perrypetiet/EasyDSP/device_firmware/main/dsp_defines/sigma_dsp_module_data.h

#ifndef SIGMA_DSP_MODULE_DATA_H_
#define SIGMA_DSP_MODULE_DATA_H_

#define ADA_COEFFICIENT_AMOUNT                   5

/* Module input1_eq - Medium Size Eq*/
#define MOD_INPUT1_EQ_COUNT                      25
#define MOD_INPUT1_EQ_ALG0_STAGE0_B0_ADDR        0
#define MOD_INPUT1_EQ_ALG0_STAGE0_B0_FIXPT       0x00800000
#define MOD_INPUT1_EQ_ALG0_STAGE0_B1_ADDR        1
#define MOD_INPUT1_EQ_ALG0_STAGE0_B1_FIXPT       0x00000000
#define MOD_INPUT1_EQ_ALG0_STAGE0_B2_ADDR        2
#define MOD_INPUT1_EQ_ALG0_STAGE0_B2_FIXPT       0x00000000
#define MOD_INPUT1_EQ_ALG0_STAGE0_A0_ADDR        3
#define MOD_INPUT1_EQ_ALG0_STAGE0_A0_FIXPT       0x00000000
#define MOD_INPUT1_EQ_ALG0_STAGE0_A1_ADDR        4
#define MOD_INPUT1_EQ_ALG0_STAGE0_A1_FIXPT       0x00000000
#define MOD_INPUT1_EQ_ALG0_STAGE1_B0_ADDR        5
#define MOD_INPUT1_EQ_ALG0_STAGE1_B0_FIXPT       0x00800000
#define MOD_INPUT1_EQ_ALG0_STAGE1_B1_ADDR        6
#define MOD_INPUT1_EQ_ALG0_STAGE1_B1_FIXPT       0x00000000
#define MOD_INPUT1_EQ_ALG0_STAGE1_B2_ADDR        7
#define MOD_INPUT1_EQ_ALG0_STAGE1_B2_FIXPT       0x00000000
#define MOD_INPUT1_EQ_ALG0_STAGE1_A0_ADDR        8
#define MOD_INPUT1_EQ_ALG0_STAGE1_A0_FIXPT       0x00000000
#define MOD_INPUT1_EQ_ALG0_STAGE1_A1_ADDR        9
#define MOD_INPUT1_EQ_ALG0_STAGE1_A1_FIXPT       0x00000000
#define MOD_INPUT1_EQ_ALG0_STAGE2_B0_ADDR        10
#define MOD_INPUT1_EQ_ALG0_STAGE2_B0_FIXPT       0x00800000
#define MOD_INPUT1_EQ_ALG0_STAGE2_B1_ADDR        11
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
#define MOD_OUTPUT4_EQ_ALG0_STAGE3_B2_ADDR       147
#define MOD_OUTPUT4_EQ_ALG0_STAGE3_B2_FIXPT      0x00000000
#define MOD_OUTPUT4_EQ_ALG0_STAGE3_A0_ADDR       148
#define MOD_OUTPUT4_EQ_ALG0_STAGE3_A0_FIXPT      0x00000000
#define MOD_OUTPUT4_EQ_ALG0_STAGE3_A1_ADDR       149
#define MOD_OUTPUT4_EQ_ALG0_STAGE3_A1_FIXPT      0x00000000
#define MOD_OUTPUT4_EQ_ALG0_STAGE4_B0_ADDR       150
#define MOD_OUTPUT4_EQ_ALG0_STAGE4_B0_FIXPT      0x00800000
#define MOD_OUTPUT4_EQ_ALG0_STAGE4_B1_ADDR       151
#define MOD_OUTPUT4_EQ_ALG0_STAGE4_B1_FIXPT      0x00000000
#define MOD_OUTPUT4_EQ_ALG0_STAGE4_B2_ADDR       152
#define MOD_OUTPUT4_EQ_ALG0_STAGE4_B2_FIXPT      0x00000000
#define MOD_OUTPUT4_EQ_ALG0_STAGE4_A0_ADDR       153
#define MOD_OUTPUT4_EQ_ALG0_STAGE4_A0_FIXPT      0x00000000
#define MOD_OUTPUT4_EQ_ALG0_STAGE4_A1_ADDR       154
#define MOD_OUTPUT4_EQ_ALG0_STAGE4_A1_FIXPT      0x00000000
/* Module output1_gain - Single SW slew vol (adjustable)*/
#define MOD_OUTPUT1_GAIN_COUNT             2
#define MOD_OUTPUT1_GAIN_ALG0_TARGET_ADDR        155
#define MOD_OUTPUT1_GAIN_ALG0_TARGET_FIXPT       0x00800000
#define MOD_OUTPUT1_GAIN_ALG0_STEP_ADDR        156
#define MOD_OUTPUT1_GAIN_ALG0_STEP_FIXPT         0x00000800
/* Module output2_gain - Single SW slew vol (adjustable)*/
#define MOD_OUTPUT2_GAIN_COUNT             2
#define MOD_OUTPUT2_GAIN_ALG0_TARGET_ADDR        157
#define MOD_OUTPUT2_GAIN_ALG0_TARGET_FIXPT       0x00800000
#define MOD_OUTPUT2_GAIN_ALG0_STEP_ADDR        158
#define MOD_OUTPUT2_GAIN_ALG0_STEP_FIXPT         0x00000800
/* Module output3_gain - Single SW slew vol (adjustable)*/
#define MOD_OUTPUT3_GAIN_COUNT             2
#define MOD_OUTPUT3_GAIN_ALG0_TARGET_ADDR        159
#define MOD_OUTPUT3_GAIN_ALG0_TARGET_FIXPT       0x00800000
#define MOD_OUTPUT3_GAIN_ALG0_STEP_ADDR        160
#define MOD_OUTPUT3_GAIN_ALG0_STEP_FIXPT         0x00000800
/* Module output4_gain - Single SW slew vol (adjustable)*/
#define MOD_OUTPUT4_GAIN_COUNT             2
#define MOD_OUTPUT4_GAIN_ALG0_TARGET_ADDR        161
#define MOD_OUTPUT4_GAIN_ALG0_TARGET_FIXPT       0x00800000
#define MOD_OUTPUT4_GAIN_ALG0_STEP_ADDR        162
#define MOD_OUTPUT4_GAIN_ALG0_STEP_FIXPT         0x00000800


#endif /* SIGMA_DSP_MODULE_DATA_H_ */
