perrypetiet/EasyDSP/device_firmware/sigma_studio_project/export/easydsp_IC_1.h

/*
 * File:           C:\Users\perry\Documents\GitHub\EasyDSP\device_firmware\sigma_studio_project\export\easydsp_IC_1.h
 *
 * Created:        Thursday, November 9, 2023 1:23:58 PM
 * Description:    easydsp:IC 1 program data.
 *
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
 * This software may only be used to program products purchased from
 * Analog Devices for incorporation by you into audio products that
 * are intended for resale to audio product end users. This software
 * may not be distributed whole or in any part to third parties.
 *
 * Copyright ©2023 Analog Devices, Inc. All rights reserved.
 */
#ifndef __EASYDSP_IC_1_H__
#define __EASYDSP_IC_1_H__

#include "SigmaStudioFW.h"
#include "easydsp_IC_1_REG.h"

#define DEVICE_ARCHITECTURE_IC_1                  "ADAU1701"
#define DEVICE_ADDR_IC_1                          0x68

/* DSP Program Data */
#define PROGRAM_SIZE_IC_1 5120
#define PROGRAM_ADDR_IC_1 1024
ADI_REG_TYPE Program_Data_IC_1[PROGRAM_SIZE_IC_1] = {
0x00, 0x00, 0x00, 0x00, 0x01, 
0x00, 0x10, 0x00, 0xE8, 0x01, 
0x00, 0x00, 0x00, 0x00, 0x01, 
0x01, 0x18, 0x00, 0xE8, 0x01, 
0x00, 0x3A, 0x03, 0x20, 0x01, 
0x00, 0x32, 0x04, 0x22, 0x01, 
0x00, 0x22, 0x03, 0x34, 0x01, 
0x00, 0x1A, 0x04, 0x22, 0x01, 
0x00, 0x12, 0x00, 0x22, 0x01, 
0x00, 0x0A, 0x01, 0x22, 0x01, 
0x00, 0x02, 0x02, 0x22, 0x01, 
0x00, 0x00, 0x00, 0x00, 0x01, 
0x00, 0x28, 0x00, 0xE2, 0x01, 
0x00, 0x40, 0x00, 0xF2, 0x01, 
0x00, 0x6A, 0x08, 0x20, 0x01, 
0x00, 0x62, 0x09, 0x22, 0x01, 
0x00, 0x52, 0x08, 0x34, 0x01, 
0x00, 0x4A, 0x09, 0x22, 0x01, 
0x00, 0x2A, 0x05, 0x22, 0x01, 
0x00, 0x22, 0x06, 0x22, 0x01, 
0x00, 0x1A, 0x07, 0x22, 0x01, 
0x00, 0x00, 0x00, 0x00, 0x01, 
0x00, 0x58, 0x00, 0xE2, 0x01, 
0x00, 0x70, 0x00, 0xF2, 0x01, 
0x00, 0x9A, 0x0D, 0x20, 0x01, 
0x00, 0x92, 0x0E, 0x22, 0x01, 
0x00, 0x82, 0x0D, 0x34, 0x01, 
0x00, 0x7A, 0x0E, 0x22, 0x01, 
0x00, 0x5A, 0x0A, 0x22, 0x01, 
0x00, 0x52, 0x0B, 0x22, 0x01, 
0x00, 0x4A, 0x0C, 0x22, 0x01, 
0x00, 0x00, 0x00, 0x00, 0x01, 
0x00, 0x88, 0x00, 0xE2, 0x01, 
0x00, 0xA0, 0x00, 0xF2, 0x01, 
0x00, 0xCA, 0x12, 0x20, 0x01, 
0x00, 0xC2, 0x13, 0x22, 0x01, 
0x00, 0xB2, 0x12, 0x34, 0x01, 
0x00, 0xAA, 0x13, 0x22, 0x01, 
0x00, 0x8A, 0x0F, 0x22, 0x01, 
0x00, 0x82, 0x10, 0x22, 0x01, 
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
};

/* DSP Parameter (Coefficient) Data */
#define PARAM_SIZE_IC_1 4096
#define PARAM_ADDR_IC_1 0
ADI_REG_TYPE Param_Data_IC_1[PARAM_SIZE_IC_1] = {
0x00, 0x80, 0x00, 0x00, 
0x00, 0x00, 0x00, 0x00, 
0x00, 0x00, 0x00, 0x00, 
0x00, 0x00, 0x00, 0x00, 
0x00, 0x00, 0x00, 0x00, 
0x00, 0x80, 0x00, 0x00, 
0x00, 0x00, 0x00, 0x00, 
0x00, 0x00, 0x00, 0x00, 
0x00, 0x00, 0x00, 0x00, 
0x00, 0x00, 0x00, 0x00, 
0x00, 0x80, 0x00, 0x00, 
0x00, 0x00, 0x00, 0x00, 
0x00, 0x00, 0x00, 0x00, 
0x00, 0x00, 0x00, 0x00, 
0x00, 0x00, 0x00, 0x00, 
0x00, 0x80, 0x00, 0x00, 
0x00, 0x00, 0x00, 0x00, 
0x00, 0x00, 0x00, 0x00, 
0x00, 0x00, 0x00, 0x00, 
0x00, 0x00, 0x00, 0x00, 
0x00, 0x80, 0x00, 0x00, 
0x00, 0x00, 0x00, 0x00, 
0x00, 0x00, 0x00, 0x00, 
0x00, 0x00, 0x00, 0x00, 
0x00, 0x00, 0x00, 0x00, 
0x00, 0x80, 0x00, 0x00, 
0x00, 0x00, 0x00, 0x00, 
0x00, 0x00, 0x00, 0x00, 
0x00, 0x00, 0x00, 0x00, 
0x00, 0x00, 0x00, 0x00, 
0x00, 0x80, 0x00, 0x00, 
0x00, 0x00, 0x00, 0x00, 
0x00, 0x00, 0x00, 0x00, 
0x00, 0x00, 0x00, 0x00, 
0x00, 0x00, 0x00, 0x00, 
0x00, 0x80, 0x00, 0x00, 
0x00, 0x00, 0x00, 0x00, 
0x00, 0x00, 0x00, 0x00, 
0x00, 0x00, 0x00, 0x00, 
0x00, 0x00, 0x00, 0x00, 
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
};


/* Register Default - IC 1.CoreRegister */
ADI_REG_TYPE R0_COREREGISTER_IC_1_Default[REG_COREREGISTER_IC_1_BYTE] = {
0x00, 0x18
};

/* Register Default - IC 1.HWConFiguration */
#define R3_HWCONFIGURATION_IC_1_SIZE 24
ADI_REG_TYPE R3_HWCONFIGURATION_IC_1_Default[R3_HWCONFIGURATION_IC_1_SIZE] = {
0x00, 0x18, 0x08, 0x00, 0x00, 0x00, 0x00, 0x00, 0x00, 0x00, 0x00, 0x00, 0x00, 0x00, 0x00, 0x00, 0x80, 0x00, 0x00, 0x00, 0x00, 0x00, 0x00, 0x01
};

/* Register Default - IC 1.CoreRegister */
ADI_REG_TYPE R4_COREREGISTER_IC_1_Default[REG_COREREGISTER_IC_1_BYTE] = {
0x00, 0x1C
};


/*
 * Default Download
 */
#define DEFAULT_DOWNLOAD_SIZE_IC_1 5

void default_download_IC_1() {
	SIGMA_WRITE_REGISTER_BLOCK( DEVICE_ADDR_IC_1, REG_COREREGISTER_IC_1_ADDR, REG_COREREGISTER_IC_1_BYTE, R0_COREREGISTER_IC_1_Default );
	SIGMA_WRITE_REGISTER_BLOCK( DEVICE_ADDR_IC_1, PROGRAM_ADDR_IC_1, PROGRAM_SIZE_IC_1, Program_Data_IC_1 );
	SIGMA_WRITE_REGISTER_BLOCK( DEVICE_ADDR_IC_1, PARAM_ADDR_IC_1, PARAM_SIZE_IC_1, Param_Data_IC_1 );
	SIGMA_WRITE_REGISTER_BLOCK( DEVICE_ADDR_IC_1, REG_COREREGISTER_IC_1_ADDR , R3_HWCONFIGURATION_IC_1_SIZE, R3_HWCONFIGURATION_IC_1_Default );
	SIGMA_WRITE_REGISTER_BLOCK( DEVICE_ADDR_IC_1, REG_COREREGISTER_IC_1_ADDR, REG_COREREGISTER_IC_1_BYTE, R4_COREREGISTER_IC_1_Default );
}

#endif
