perrypetiet/EasyDSP/device_firmware/main/crc16.c

/*
 * Library: libcrc
 * File:    src/crc16.c
 * Author:  Lammert Bies
 *
 * This file is licensed under the MIT License as stated below
 *
 * Copyright (c) 1999-2016 Lammert Bies
 *
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
 * Description
 * -----------
 * The source file src/crc16.c contains routines which calculate the common
 * CRC16 cyclic redundancy check values for an incomming byte string.
 */

#include <stdbool.h>
#include <stdlib.h>
#include "crc16.h"

static void             init_crc16_tab( void );

static bool             crc_tab16_init          = false;
static uint16_t         crc_tab16[256];

/*
 * uint16_t crc_16( const unsigned char *input_str, size_t num_bytes );
 *
 * The function crc_16() calculates the 16 bits CRC16 in one pass for a byte
 * string of which the beginning has been passed to the function. The number of
 * bytes to check is also a parameter. The number of the bytes in the string is
 * limited by the constant SIZE_MAX.
 */

uint16_t crc_16( const unsigned char *input_str, size_t num_bytes ) {

	uint16_t crc;
	const unsigned char *ptr;
	size_t a;

	if ( ! crc_tab16_init ) init_crc16_tab();

	crc = CRC_START_16;
	ptr = input_str;

	if ( ptr != NULL ) for (a=0; a<num_bytes; a++) {

		crc = (crc >> 8) ^ crc_tab16[ (crc ^ (uint16_t) *ptr++) & 0x00FF ];
	}

	return crc;

}  /* crc_16 */

/*
 * uint16_t crc_modbus( const unsigned char *input_str, size_t num_bytes );
 *
 * The function crc_modbus() calculates the 16 bits Modbus CRC in one pass for
 * a byte string of which the beginning has been passed to the function. The
 * number of bytes to check is also a parameter.
 */

uint16_t crc_modbus( const unsigned char *input_str, size_t num_bytes ) {

	uint16_t crc;
	const unsigned char *ptr;
	size_t a;

	if ( ! crc_tab16_init ) init_crc16_tab();

	crc = CRC_START_MODBUS;
	ptr = input_str;

	if ( ptr != NULL ) for (a=0; a<num_bytes; a++) {

		crc = (crc >> 8) ^ crc_tab16[ (crc ^ (uint16_t) *ptr++) & 0x00FF ];
	}

	return crc;

}  /* crc_modbus */

/*
 * uint16_t update_crc_16( uint16_t crc, unsigned char c );
 *
 * The function update_crc_16() calculates a new CRC-16 value based on the
 * previous value of the CRC and the next byte of data to be checked.
 */

uint16_t update_crc_16( uint16_t crc, unsigned char c ) {

	if ( ! crc_tab16_init ) init_crc16_tab();

	return (crc >> 8) ^ crc_tab16[ (crc ^ (uint16_t) c) & 0x00FF ];

}  /* update_crc_16 */

/*
 * static void init_crc16_tab( void );
 *
 * For optimal performance uses the CRC16 routine a lookup table with values
 * that can be used directly in the XOR arithmetic in the algorithm. This
 * lookup table is calculated by the init_crc16_tab() routine, the first time
 * the CRC function is called.
 */

static void init_crc16_tab( void ) {

	uint16_t i;
	uint16_t j;
	uint16_t crc;
	uint16_t c;

	for (i=0; i<256; i++) {

		crc = 0;
		c   = i;

		for (j=0; j<8; j++) {

			if ( (crc ^ c) & 0x0001 ) crc = ( crc >> 1 ) ^ CRC_POLY_16;
			else                      crc =   crc >> 1;

			c = c >> 1;
		}

		crc_tab16[i] = crc;
	}

	crc_tab16_init = true;

}  /* init_crc16_tab */
