perrypetiet/EasyDSP/device_firmware/main/parser.c

/*
 * parser.c
 *
 * Created: 18-03-2024 
 * Author: Perry Petiet
 *
 */
/******************************* INCLUDES ********************************/

#include "parser.h"

/******************************* GLOBAL VARIABLES ************************/

/******************************* LOCAL FUNCTIONS *************************/

/******************************* GLOBAL FUNCTIONS ************************/

/******************************* THE END *********************************/
