perrypetiet/EasyDSP/device_firmware/main/parser.h

/*
 * parser.h
 *
 * Created: 18-03-2024 
 * Author: Perry Petiet
 *
 */
#ifndef PARSER_H
#define PARSER_H

/******************************* INCLUDES ********************************/

#include <stdio.h>
#include <stdbool.h>
#include <stdint.h>
#include <string.h>
#include "esp_log.h"
#include "event.h"

/******************************* DEFINES *********************************/

/******************************* TYPEDEFS ********************************/

/******************************* LOCAL FUNCTIONS *************************/

/******************************* GLOBAL FUNCTIONS ************************/

/******************************* THE END *********************************/

#endif /* PARSER_H */
